silvanalopezcuellar/VCO/VCO/VCO-PSpiceFiles/SCHEMATIC1/VCO/VCO.cir

** Profile: "SCHEMATIC1-VCO"  [ C:\Users\estudiante\Downloads\VCO\vco-pspicefiles\schematic1\vco.sim ] 

** Creating circuit file "VCO.cir" 
** WARNING: THIS AUTOMATICALLY GENERATED FILE MAY BE OVERWRITTEN BY SUBSEQUENT SIMULATIONS

*Libraries: 
* Profile Libraries :
* Local Libraries :
* From [PSPICE NETLIST] section of C:\Users\estudiante\AppData\Roaming\SPB_Data\cdssetup\OrCAD_PSpice\17.2.0\PSpice.ini file:
.lib "nom.lib" 

*Analysis directives: 
.TRAN  0 100m 0 0.1m 
.OPTIONS ADVCONV
.PROBE64 V(alias(*)) I(alias(*)) W(alias(*)) D(alias(*)) NOISE(alias(*)) 
.INC "..\SCHEMATIC1.net" 


.END
